ECEBORG/DontDry_An_Intro_To_Electronics_and_IoT/Photos d'illustration/IMG_9422.JPG

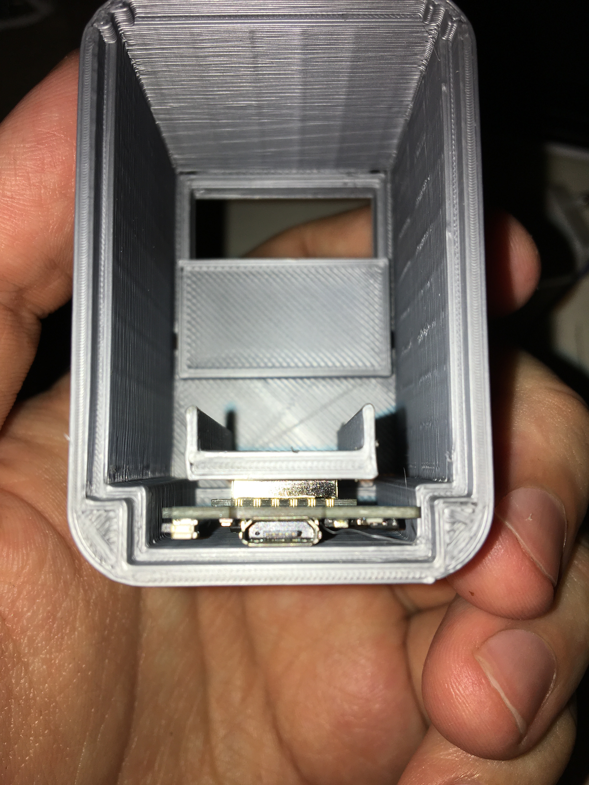
Photos d'illustration/IMG_9422.JPG
